mkdsfm/LumaBloom/hardware/3d-print/source/BR-009-3D - Bud.step

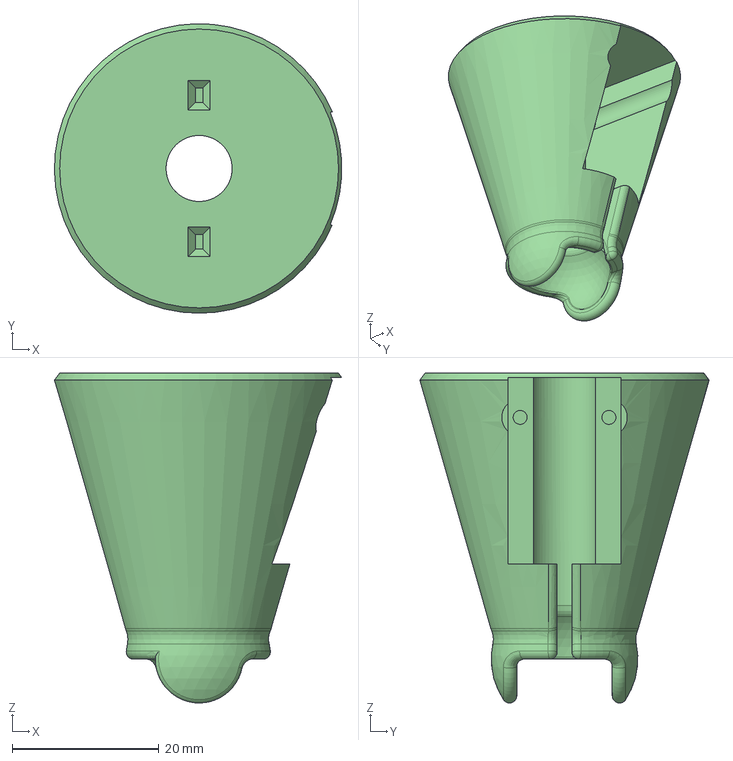
[picture p21: CAD file, 2026-07-01]
hardware/3d-print/source/BR-009-3D - Bud.step
39.1 x 39.4 x 45.0 mm
