mkdsfm/LumaBloom/hardware/3d-print/source/BR-010-3D - Flower disk V2.step

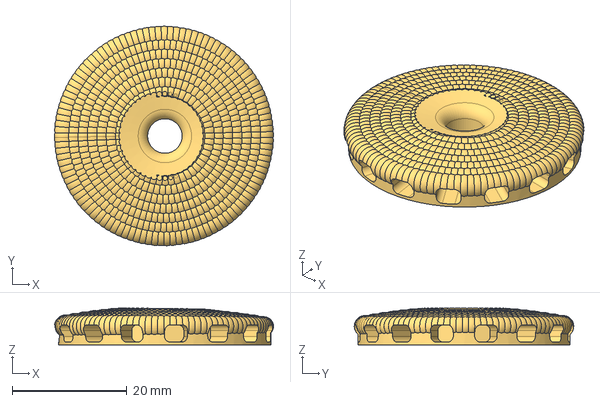
[picture p22: CAD file, 2026-07-01]
hardware/3d-print/source/BR-010-3D - Flower disk V2.step
38.1 x 38.2 x 6.42 mm
