mkdsfm/LumaBloom/hardware/3d-print/source/BR-004-3D Wase.step

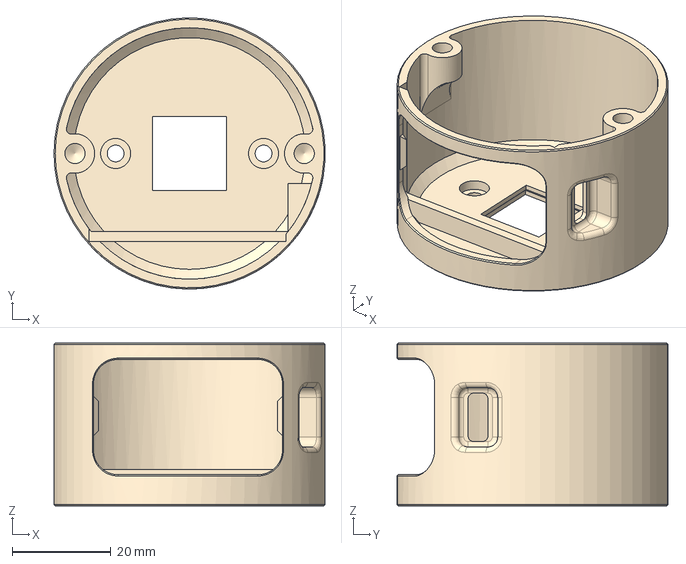
[picture p23: CAD file, 2026-07-01]
hardware/3d-print/source/BR-004-3D Wase.step
55.0 x 55.0 x 33.0 mm
