mkdsfm/LumaBloom/hardware/3d-print/source/BR-002-3D - Ball joint Mid.step

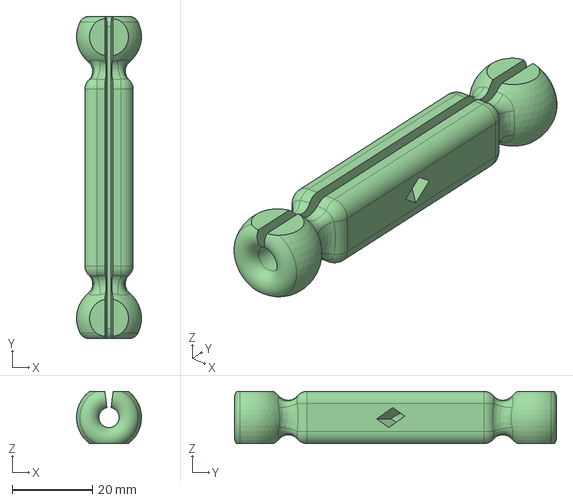
[picture p24: CAD file, 2026-07-01]
hardware/3d-print/source/BR-002-3D - Ball joint Mid.step
16.1 x 80.0 x 13.0 mm
