mkdsfm/LumaBloom/hardware/3d-print/source/BR-001-3D - Ball joint.step

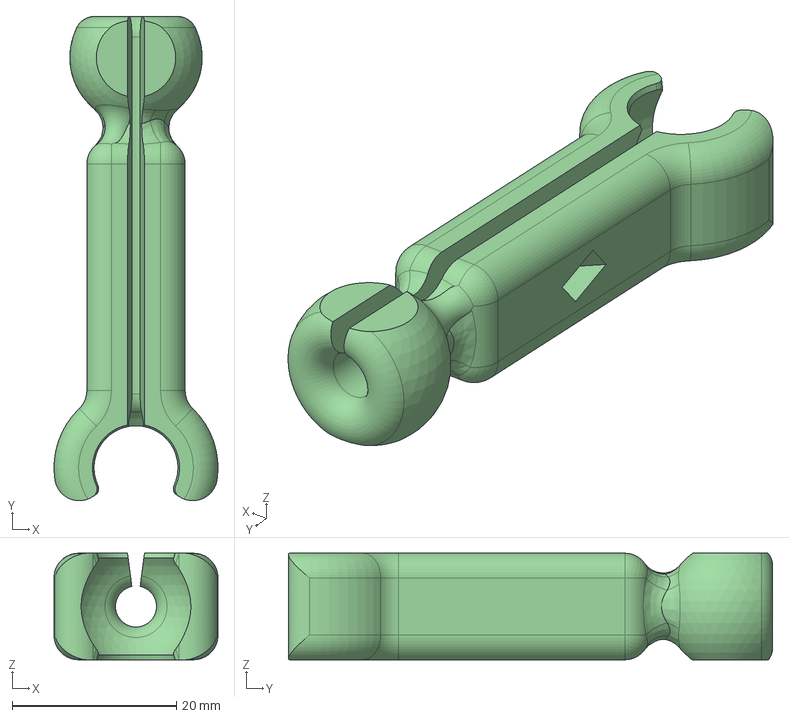
[picture p25: CAD file, 2026-07-01]
hardware/3d-print/source/BR-001-3D - Ball joint.step
20.0 x 59.0 x 13.0 mm
