mkdsfm/LumaBloom/firmware/firmware_esp32c6/main/display_lcd.c

#include "display_lcd.h"

#include <stdbool.h>
#include <stdint.h>
#include <string.h>

#include "app_config.h"
#include "driver/gpio.h"
#include "driver/ledc.h"
#include "driver/spi_master.h"
#include "esp_check.h"
#include "esp_heap_caps.h"
#include "esp_lcd_panel_io.h"
#include "esp_lcd_panel_ops.h"
#include "esp_lcd_panel_vendor.h"
#include "esp_log.h"

static const char *TAG = "display_lcd";

static const ledc_mode_t BACKLIGHT_LEDC_MODE = LEDC_LOW_SPEED_MODE;
static const ledc_timer_t BACKLIGHT_LEDC_TIMER = LEDC_TIMER_0;
static const ledc_channel_t BACKLIGHT_LEDC_CHANNEL = LEDC_CHANNEL_0;
static const ledc_timer_bit_t BACKLIGHT_LEDC_RESOLUTION = LEDC_TIMER_10_BIT;
static const int BACKLIGHT_LEDC_FREQUENCY_HZ = 5000;
static const int BACKLIGHT_LEDC_MAX_DUTY = (1 << 10) - 1;

static uint16_t color_to_panel_bytes(uint16_t color)
{
    // ESP32 stores uint16_t little-endian, but ST7789 consumes RGB565/BGR565
    // pixels MSB first over SPI. Without this swap some purples appear yellow.
    return (uint16_t)((color << 8) | (color >> 8));
}

typedef struct {
    esp_lcd_panel_io_handle_t io_handle;
    esp_lcd_panel_handle_t panel_handle;
    uint16_t *framebuffer;
    bool ready;
} lcd_state_t;

static lcd_state_t s_lcd;

static int clamp_backlight_percent(int percent)
{
    if (percent < 0) {
        return 0;
    }
    if (percent > 100) {
        return 100;
    }
    return percent;
}

static esp_err_t configure_backlight(void)
{
    const int percent = clamp_backlight_percent(APP_LCD_BACKLIGHT_PERCENT);
    const uint32_t duty = (uint32_t)((BACKLIGHT_LEDC_MAX_DUTY * percent) / 100);

    const ledc_timer_config_t timer_config = {
        .speed_mode = BACKLIGHT_LEDC_MODE,
        .duty_resolution = BACKLIGHT_LEDC_RESOLUTION,
        .timer_num = BACKLIGHT_LEDC_TIMER,
        .freq_hz = BACKLIGHT_LEDC_FREQUENCY_HZ,
        .clk_cfg = LEDC_AUTO_CLK,
    };
    ESP_RETURN_ON_ERROR(ledc_timer_config(&timer_config), TAG, "backlight ledc_timer_config failed");

    const ledc_channel_config_t channel_config = {
        .gpio_num = APP_LCD_BL,
        .speed_mode = BACKLIGHT_LEDC_MODE,
        .channel = BACKLIGHT_LEDC_CHANNEL,
        .intr_type = LEDC_INTR_DISABLE,
        .timer_sel = BACKLIGHT_LEDC_TIMER,
        .duty = duty,
        .hpoint = 0,
    };
    ESP_RETURN_ON_ERROR(ledc_channel_config(&channel_config), TAG, "backlight ledc_channel_config failed");

    ESP_LOGI(TAG, "LCD backlight set to %d%%", percent);
    return ESP_OK;
}

typedef struct {
    char c;
    uint8_t columns[5];
} glyph_t;

static const glyph_t kGlyphs[] = {
    {' ', {0x00, 0x00, 0x00, 0x00, 0x00}},
    {'-', {0x08, 0x08, 0x08, 0x08, 0x08}},
    {'.', {0x00, 0x00, 0x00, 0x18, 0x18}},
    {'%', {0x63, 0x64, 0x08, 0x13, 0x63}},
    {'/', {0x03, 0x04, 0x08, 0x10, 0x60}},
    {':', {0x00, 0x18, 0x18, 0x00, 0x18}},
    {'0', {0x3E, 0x45, 0x49, 0x51, 0x3E}},
    {'1', {0x00, 0x21, 0x7F, 0x01, 0x00}},
    {'2', {0x23, 0x45, 0x49, 0x51, 0x21}},
    {'3', {0x42, 0x41, 0x51, 0x69, 0x46}},
    {'4', {0x0C, 0x14, 0x24, 0x7F, 0x04}},
    {'5', {0x72, 0x51, 0x51, 0x51, 0x4E}},
    {'6', {0x1E, 0x29, 0x49, 0x49, 0x06}},
    {'7', {0x40, 0x47, 0x48, 0x50, 0x60}},
    {'8', {0x36, 0x49, 0x49, 0x49, 0x36}},
    {'9', {0x30, 0x49, 0x49, 0x4A, 0x3C}},
    {'A', {0x1F, 0x24, 0x44, 0x24, 0x1F}},
    {'B', {0x7F, 0x49, 0x49, 0x49, 0x36}},
    {'C', {0x3E, 0x41, 0x41, 0x41, 0x22}},
    {'D', {0x7F, 0x41, 0x41, 0x22, 0x1C}},
    {'E', {0x7F, 0x49, 0x49, 0x49, 0x41}},
    {'H', {0x7F, 0x08, 0x08, 0x08, 0x7F}},
    {'I', {0x00, 0x41, 0x7F, 0x41, 0x00}},
    {'J', {0x02, 0x01, 0x01, 0x01, 0x7E}},
    {'K', {0x7F, 0x08, 0x14, 0x22, 0x41}},
    {'L', {0x7F, 0x01, 0x01, 0x01, 0x01}},
    {'M', {0x7F, 0x20, 0x10, 0x20, 0x7F}},
    {'N', {0x7F, 0x10, 0x08, 0x04, 0x7F}},
    {'O', {0x3E, 0x41, 0x41, 0x41, 0x3E}},
    {'P', {0x7F, 0x48, 0x48, 0x48, 0x30}},
    {'R', {0x7F, 0x48, 0x4C, 0x4A, 0x31}},
    {'S', {0x31, 0x49, 0x49, 0x49, 0x46}},
    {'T', {0x40, 0x40, 0x7F, 0x40, 0x40}},
    {'U', {0x7E, 0x01, 0x01, 0x01, 0x7E}},
    {'V', {0x7C, 0x02, 0x01, 0x02, 0x7C}},
    {'W', {0x7F, 0x02, 0x04, 0x02, 0x7F}},
    {'X', {0x63, 0x14, 0x08, 0x14, 0x63}},
    {'Y', {0x70, 0x08, 0x07, 0x08, 0x70}},
};

int display_lcd_text_width(const char *text, int scale)
{
    if (text == NULL) {
        return 0;
    }
    return (int)strlen(text) * 6 * scale;
}

static const uint8_t *find_glyph(char c)
{
    for (size_t i = 0; i < sizeof(kGlyphs) / sizeof(kGlyphs[0]); ++i) {
        if (kGlyphs[i].c == c) {
            return kGlyphs[i].columns;
        }
    }
    return kGlyphs[0].columns;
}

static void set_pixel(int x, int y, uint16_t color)
{
    if (x < 0 || x >= APP_LCD_WIDTH || y < 0 || y >= APP_LCD_HEIGHT) {
        return;
    }
    s_lcd.framebuffer[(y * APP_LCD_WIDTH) + x] = color_to_panel_bytes(color);
}

void display_lcd_fill_screen(uint16_t color)
{
    const size_t pixels = APP_LCD_WIDTH * APP_LCD_HEIGHT;
    const uint16_t panel_color = color_to_panel_bytes(color);
    for (size_t i = 0; i < pixels; ++i) {
        s_lcd.framebuffer[i] = panel_color;
    }
}

void display_lcd_fill_rect(int x, int y, int w, int h, uint16_t color)
{
    for (int py = 0; py < h; ++py) {
        for (int px = 0; px < w; ++px) {
            set_pixel(x + px, y + py, color);
        }
    }
}

void display_lcd_draw_rect(int x, int y, int w, int h, uint16_t color)
{
    if (w <= 0 || h <= 0) {
        return;
    }

    for (int px = 0; px < w; ++px) {
        set_pixel(x + px, y, color);
        set_pixel(x + px, y + h - 1, color);
    }

    for (int py = 0; py < h; ++py) {
        set_pixel(x, y + py, color);
        set_pixel(x + w - 1, y + py, color);
    }
}

void display_lcd_draw_line(int x0, int y0, int x1, int y1, uint16_t color)
{
    int dx = (x1 > x0) ? (x1 - x0) : (x0 - x1);
    int sx = (x0 < x1) ? 1 : -1;
    int dy = -((y1 > y0) ? (y1 - y0) : (y0 - y1));
    int sy = (y0 < y1) ? 1 : -1;
    int err = dx + dy;

    while (true) {
        set_pixel(x0, y0, color);
        if (x0 == x1 && y0 == y1) {
            break;
        }

        int e2 = err * 2;
        if (e2 >= dy) {
            err += dy;
            x0 += sx;
        }
        if (e2 <= dx) {
            err += dx;
            y0 += sy;
        }
    }
}

void display_lcd_draw_circle(int center_x, int center_y, int radius, uint16_t color)
{
    if (radius < 0) {
        return;
    }

    int x = radius;
    int y = 0;
    int err = 1 - x;

    while (x >= y) {
        set_pixel(center_x + x, center_y + y, color);
        set_pixel(center_x + y, center_y + x, color);
        set_pixel(center_x - y, center_y + x, color);
        set_pixel(center_x - x, center_y + y, color);
        set_pixel(center_x - x, center_y - y, color);
        set_pixel(center_x - y, center_y - x, color);
        set_pixel(center_x + y, center_y - x, color);
        set_pixel(center_x + x, center_y - y, color);

        ++y;
        if (err < 0) {
            err += (2 * y) + 1;
        } else {
            --x;
            err += (2 * (y - x)) + 1;
        }
    }
}

static void draw_char(int x, int y, char c, uint16_t color, int scale)
{
    const uint8_t *glyph = find_glyph(c);
    for (int col = 0; col < 5; ++col) {
        uint8_t bits = glyph[col];
        for (int row = 0; row < 7; ++row) {
            if (bits & (1U << row)) {
                display_lcd_fill_rect(x + (col * scale), y + (row * scale), scale, scale, color);
            }
        }
    }
}

void display_lcd_draw_text(int x, int y, const char *text, uint16_t color, int scale)
{
    if (text == NULL) {
        return;
    }

    int cursor_x = x;
    for (size_t i = 0; text[i] != '\0'; ++i) {
        draw_char(cursor_x, y, text[i], color, scale);
        cursor_x += 6 * scale;
    }
}

void display_lcd_draw_text_outlined(
    int x,
    int y,
    const char *text,
    uint16_t color,
    uint16_t outline_color,
    int scale)
{
    // Eight one-pixel copies form a crisp outline around the 5x7 pixel font.
    // Change the offset range only if a thicker outline is intentionally wanted.
    for (int offset_y = -1; offset_y <= 1; ++offset_y) {
        for (int offset_x = -1; offset_x <= 1; ++offset_x) {
            if (offset_x == 0 && offset_y == 0) {
                continue;
            }
            display_lcd_draw_text(x + offset_x, y + offset_y, text, outline_color, scale);
        }
    }
    display_lcd_draw_text(x, y, text, color, scale);
}

void display_lcd_draw_text_centered(int center_x, int y, const char *text, uint16_t color, int scale)
{
    display_lcd_draw_text(center_x - (display_lcd_text_width(text, scale) / 2), y, text, color, scale);
}

void display_lcd_draw_text_right(int right_x, int y, const char *text, uint16_t color, int scale)
{
    display_lcd_draw_text(right_x - display_lcd_text_width(text, scale), y, text, color, scale);
}

esp_err_t display_lcd_draw_indexed_2x(
    const uint8_t *pixels,
    int source_width,
    int source_height,
    const uint16_t *palette,
    size_t palette_size)
{
    ESP_RETURN_ON_FALSE(pixels != NULL, ESP_ERR_INVALID_ARG, TAG, "indexed pixels are null");
    ESP_RETURN_ON_FALSE(palette != NULL, ESP_ERR_INVALID_ARG, TAG, "indexed palette is null");
    ESP_RETURN_ON_FALSE(
        source_width * 2 == APP_LCD_WIDTH && source_height * 2 == APP_LCD_HEIGHT,
        ESP_ERR_INVALID_SIZE,
        TAG,
        "indexed sprite dimensions do not fill LCD");

    for (int source_y = 0; source_y < source_height; ++source_y) {
        for (int source_x = 0; source_x < source_width; ++source_x) {
            uint8_t palette_index = pixels[(source_y * source_width) + source_x];
            ESP_RETURN_ON_FALSE(
                palette_index < palette_size,
                ESP_ERR_INVALID_ARG,
                TAG,
                "indexed sprite palette index is invalid");

            uint16_t color = palette[palette_index];
            int destination_x = source_x * 2;
            // Flip source Y into the framebuffer orientation and expand each
            // 160x86 source pixel into a sharp 2x2 block on the 320x172 LCD.
            int destination_y = APP_LCD_HEIGHT - ((source_y + 1) * 2);
            set_pixel(destination_x, destination_y, color);
            set_pixel(destination_x + 1, destination_y, color);
            set_pixel(destination_x, destination_y + 1, color);
            set_pixel(destination_x + 1, destination_y + 1, color);
        }
    }

    return ESP_OK;
}

esp_err_t display_lcd_flush(void)
{
    return esp_lcd_panel_draw_bitmap(
        s_lcd.panel_handle,
        0,
        0,
        APP_LCD_WIDTH,
        APP_LCD_HEIGHT,
        s_lcd.framebuffer);
}

esp_err_t display_lcd_init(void)
{
    s_lcd.framebuffer = heap_caps_calloc(
        APP_LCD_WIDTH * APP_LCD_HEIGHT,
        sizeof(uint16_t),
        MALLOC_CAP_8BIT);
    ESP_RETURN_ON_FALSE(s_lcd.framebuffer != NULL, ESP_ERR_NO_MEM, TAG, "framebuffer allocation failed");

    const spi_bus_config_t bus_config = {
        .sclk_io_num = APP_LCD_SPI_CLK,
        .mosi_io_num = APP_LCD_SPI_MOSI,
        .miso_io_num = GPIO_NUM_NC,
        .quadwp_io_num = GPIO_NUM_NC,
        .quadhd_io_num = GPIO_NUM_NC,
        .max_transfer_sz = APP_LCD_WIDTH * APP_LCD_HEIGHT * sizeof(uint16_t),
    };
    ESP_RETURN_ON_ERROR(spi_bus_initialize(APP_LCD_HOST, &bus_config, SPI_DMA_CH_AUTO), TAG, "spi_bus_initialize failed");

    const esp_lcd_panel_io_spi_config_t io_config = {
        .dc_gpio_num = APP_LCD_DC,
        .cs_gpio_num = APP_LCD_CS,
        .pclk_hz = APP_LCD_PIXEL_CLOCK_HZ,
        .lcd_cmd_bits = 8,
        .lcd_param_bits = 8,
        .spi_mode = 0,
        .trans_queue_depth = 10,
    };
    ESP_RETURN_ON_ERROR(
        esp_lcd_new_panel_io_spi((esp_lcd_spi_bus_handle_t)APP_LCD_HOST, &io_config, &s_lcd.io_handle),
        TAG,
        "esp_lcd_new_panel_io_spi failed");

    const esp_lcd_panel_dev_config_t panel_config = {
        .reset_gpio_num = APP_LCD_RST,
        .bits_per_pixel = 16,
        .rgb_ele_order = LCD_RGB_ELEMENT_ORDER_BGR,
    };
    #if defined(APP_LCD_CONTROLLER_ST7789)
        ESP_RETURN_ON_ERROR(esp_lcd_new_panel_st7789(s_lcd.io_handle, &panel_config, &s_lcd.panel_handle), TAG, "ST7789 panel creation failed");
    #elif defined(APP_LCD_CONTROLLER_JD9853)
        ESP_RETURN_ON_ERROR(esp_lcd_new_panel_st7789(s_lcd.io_handle, &panel_config, &s_lcd.panel_handle), TAG, "JD9853 panel creation failed");
        /* Разделить работу с дисплеем на общий слой и два отдельных файла lcd_st7789.c и lcd_jd9853.c 
        Добавить небольшой lcd_panel.c, который по выбранной в app_config.h модели платы подключает нужный драйвер. 
        Пины, offsets, orientation и прочие аппаратные параметры также выбирать в app_config.h в зависимости от платы */
    #else
        #error "LCD controller is not configured"
    #endif
    ESP_RETURN_ON_ERROR(esp_lcd_panel_reset(s_lcd.panel_handle), TAG, "panel reset failed");
    ESP_RETURN_ON_ERROR(esp_lcd_panel_init(s_lcd.panel_handle), TAG, "panel init failed");
    ESP_RETURN_ON_ERROR(esp_lcd_panel_swap_xy(s_lcd.panel_handle, APP_LCD_SWAP_XY), TAG, "panel swap_xy failed");
    ESP_RETURN_ON_ERROR(esp_lcd_panel_set_gap(s_lcd.panel_handle, APP_LCD_X_OFFSET, APP_LCD_Y_OFFSET), TAG, "panel set gap failed");
    ESP_RETURN_ON_ERROR(esp_lcd_panel_mirror(s_lcd.panel_handle, APP_LCD_MIRROR_X, APP_LCD_MIRROR_Y), TAG, "panel mirror failed");
    ESP_RETURN_ON_ERROR(esp_lcd_panel_invert_color(s_lcd.panel_handle, APP_LCD_INVERT_COLOR), TAG, "panel invert color failed");
    ESP_RETURN_ON_ERROR(esp_lcd_panel_disp_on_off(s_lcd.panel_handle, true), TAG, "panel on failed");
    ESP_RETURN_ON_ERROR(configure_backlight(), TAG, "backlight configure failed");
    s_lcd.ready = true;
    ESP_LOGI(TAG, "LCD ready (%dx%d, x_offset=%d, y_offset=%d)",
             APP_LCD_WIDTH, APP_LCD_HEIGHT, APP_LCD_X_OFFSET, APP_LCD_Y_OFFSET);
    return ESP_OK;
}

bool display_lcd_is_ready(void)
{
    return s_lcd.ready;
}
