mkdsfm/LumaBloom/firmware/firmware_esp32c6/main/telemetry_serial.h

#pragma once

#include "device_reading.h"

void telemetry_serial_publish(const char *protocol_id, const device_reading_t *reading);
void telemetry_serial_publish_calibration_result(bool success, float normalized_offset, const char *message);
